1000eyed/pur/source/pur-pcb/pur-offset-space-55.kicad_sch

## KiCad design source/pur-pcb/pur-offset-space-55.kicad_sch (2023-10-09)

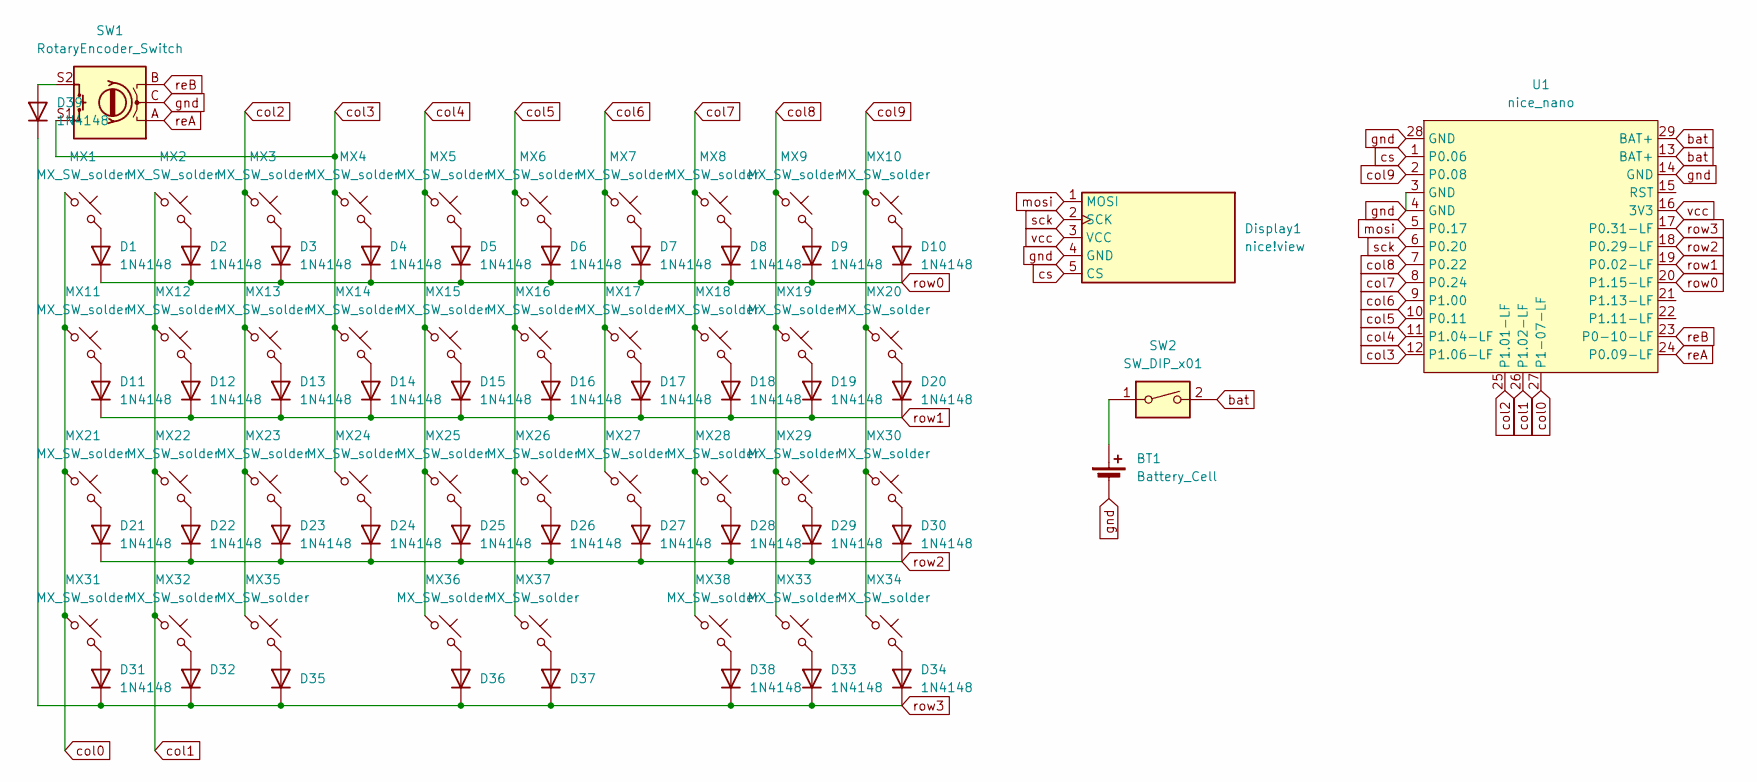
[picture p15: schematic pur-offset-space-55.kicad_sch]

Parts:
BT1: Battery_Cell; JST_PH_S2B-PH-K_1x02_P2.00mm_Horizontal
D1, D2, D3, D4, D5, D6, D7, D8, D9, D10, D11, D12, D13, D14, D15, D16, D17, D18, D19, D20, D21, D22, D23, D24, D25, D26, D27, D28, D29, D30, D31, D32, D33, D34, D35, D36, D37, D38, D39: 1N4148; D_SOD-123 invisible designator
Display1: nice!view; nice_view
MX1, MX2, MX3, MX4, MX5, MX6, MX7, MX8, MX9, MX10, MX11, MX12, MX13, MX14, MX15, MX16, MX17, MX18, MX19, MX20, MX21, MX22, MX23, MX24, MX25, MX26, MX27, MX28, MX29, MX30, MX31, MX32, MX33, MX34, MX35, MX38: MX_SW_solder; gateron-ks27
MX36, MX37: MX_SW_solder; gateron-ks27-1.75u
SW1: RotaryEncoder_Switch; ROT_Alps_EC11E-Switch
SW2: SW_DIP_x01; MSK-12C02
U1: nice_nano; nice_nano_AH_USBup

Connections:
unnamed: BT1.1 (+), SW2.1
unnamed: D1.2 (A), MX1.2
unnamed: D2.2 (A), MX2.2
unnamed: D3.2 (A), MX3.2
unnamed: D4.2 (A), MX4.2
unnamed: D5.2 (A), MX5.2
unnamed: D6.2 (A), MX6.2
unnamed: D7.2 (A), MX7.2
unnamed: D8.2 (A), MX8.2
unnamed: D9.2 (A), MX9.2
unnamed: D10.2 (A), MX10.2
unnamed: D11.2 (A), MX11.2
unnamed: D12.2 (A), MX12.2
unnamed: D13.2 (A), MX13.2
unnamed: D14.2 (A), MX14.2
unnamed: D15.2 (A), MX15.2
unnamed: D16.2 (A), MX16.2
unnamed: D17.2 (A), MX17.2
unnamed: D18.2 (A), MX18.2
unnamed: D19.2 (A), MX19.2
unnamed: D20.2 (A), MX20.2
unnamed: D21.2 (A), MX21.2
unnamed: D22.2 (A), MX22.2
unnamed: D23.2 (A), MX23.2
unnamed: D24.2 (A), MX24.2
unnamed: D25.2 (A), MX25.2
unnamed: D26.2 (A), MX26.2
unnamed: D27.2 (A), MX27.2
unnamed: D28.2 (A), MX28.2
unnamed: D29.2 (A), MX29.2
unnamed: D30.2 (A), MX30.2
unnamed: D31.2 (A), MX31.2
unnamed: D32.2 (A), MX32.2
unnamed: D33.2 (A), MX33.2
unnamed: D34.2 (A), MX34.2
unnamed: D35.2 (A), MX35.2
unnamed: D36.2 (A), MX36.2
unnamed: D37.2 (A), MX37.2
unnamed: D38.2 (A), MX38.2
unnamed: D39.2 (A), SW1.S2
bat: SW2.2, U1.13 (BAT+), U1.29 (BAT+)
col0: MX1.1, MX11.1, MX21.1, MX31.1, U1.27 (P1-07-LF)
col1: MX2.1, MX12.1, MX22.1, MX32.1, U1.26 (P1.02-LF)
col2: MX3.1, MX13.1, MX23.1, MX35.1, U1.25 (P1.01-LF)
col3: MX4.1, MX14.1, MX24.1, SW1.S1, U1.12 (P1.06-LF)
col4: MX5.1, MX15.1, MX25.1, MX36.1, U1.11 (P1.04-LF)
col5: MX6.1, MX16.1, MX26.1, MX37.1, U1.10 (P0.11)
col6: MX7.1, MX17.1, MX27.1, U1.9 (P1.00)
col7: MX8.1, MX18.1, MX28.1, MX38.1, U1.8 (P0.24)
col8: MX9.1, MX19.1, MX29.1, MX33.1, U1.7 (P0.22)
col9: MX10.1, MX20.1, MX30.1, MX34.1, U1.2 (P0.08)
cs: Display1.5 (CS), U1.1 (P0.06)
gnd: BT1.2 (-), Display1.4 (GND), SW1.C, U1.3 (GND), U1.4 (GND), U1.14 (GND), U1.28 (GND)
mosi: Display1.1 (MOSI), U1.5 (P0.17)
reA: SW1.A, U1.24 (P0.09-LF)
reB: SW1.B, U1.23 (P0-10-LF)
row0: D1.1 (K), D2.1 (K), D3.1 (K), D4.1 (K), D5.1 (K), D6.1 (K), D7.1 (K), D8.1 (K), D9.1 (K), D10.1 (K), U1.20 (P1.15-LF)
row1: D11.1 (K), D12.1 (K), D13.1 (K), D14.1 (K), D15.1 (K), D16.1 (K), D17.1 (K), D18.1 (K), D19.1 (K), D20.1 (K), U1.19 (P0.02-LF)
row2: D21.1 (K), D22.1 (K), D23.1 (K), D24.1 (K), D25.1 (K), D26.1 (K), D27.1 (K), D28.1 (K), D29.1 (K), D30.1 (K), U1.18 (P0.29-LF)
row3: D31.1 (K), D32.1 (K), D33.1 (K), D34.1 (K), D35.1 (K), D36.1 (K), D37.1 (K), D38.1 (K), D39.1 (K), U1.17 (P0.31-LF)
sck: Display1.2 (SCK), U1.6 (P0.20)
vcc: Display1.3 (VCC), U1.16 (3V3)
